jomettler/SaladFork-Experimental/InvertedMountDirectionAB/STL/Lower_B.stl

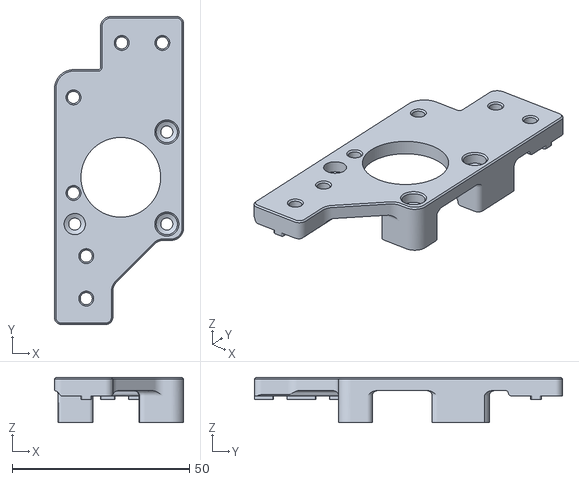
[picture p18: CAD file, 2022-04-01]
InvertedMountDirectionAB/STL/Lower_B.stl
36.5 x 87.0 x 12.8
