jomettler/SaladFork-Experimental/K3Style_Top/STL/Top/corner_10mm_x4.stl

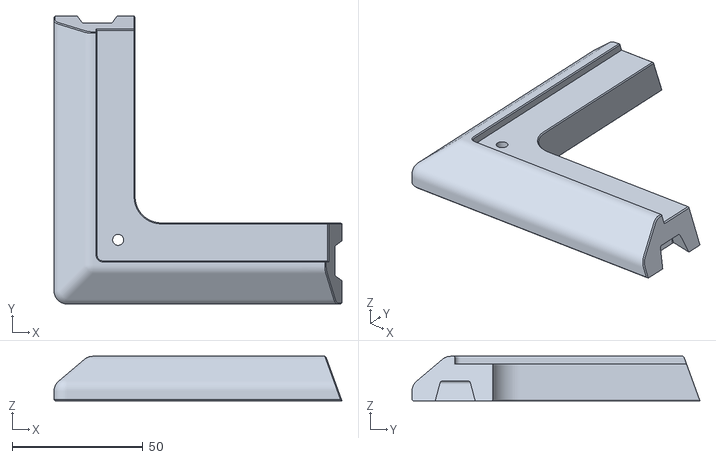
[picture p19: CAD file, 2022-04-12]
K3Style_Top/STL/Top/corner_10mm_x4.stl
110.0 x 110.0 x 17.0
