jomettler/SaladFork-Experimental/QuadAB/CAD/NOIdler_FrontDrives.step

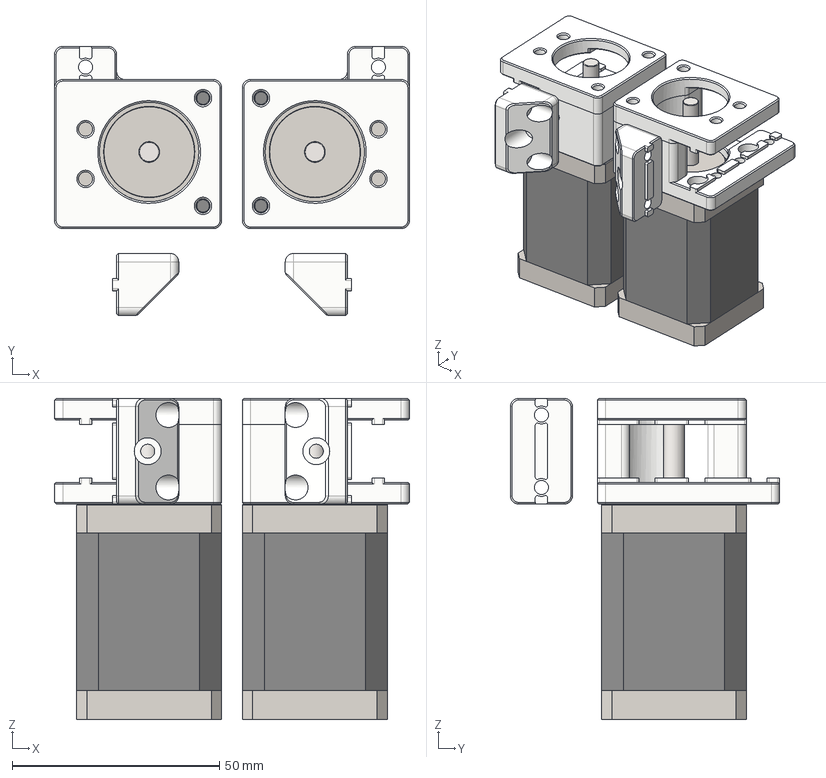
[picture p20: CAD file, 2022-04-17]
QuadAB/CAD/NOIdler_FrontDrives.step
85.7 x 65.0 x 77.5 mm
nema14_base (1) x 2
nema14_centro (1) x 2
nema14_eje (1) x 2
nema14_techo (1) x 2
