jomettler/SaladFork-Experimental/QuadAB/STL/A_Drive_Frame_Lower.stl

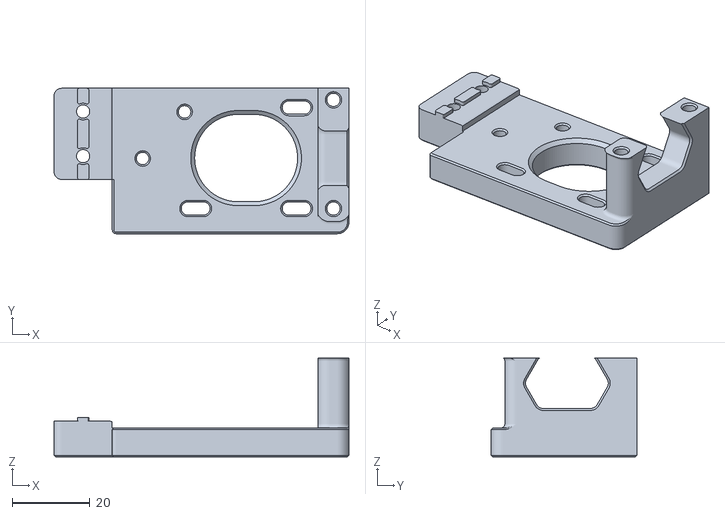
[picture p21: CAD file, 2022-03-22]
QuadAB/STL/A_Drive_Frame_Lower.stl
76.0 x 37.5 x 25.5
