jomettler/SaladFork-Experimental/QuadAB/STL/NoIdler_Front/A_Tension.stl

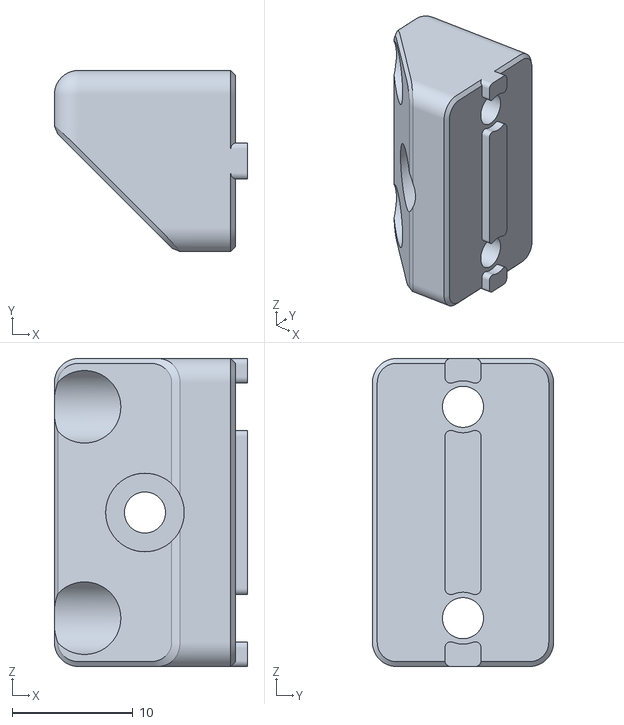
[picture p22: CAD file, 2022-04-17]
QuadAB/STL/NoIdler_Front/A_Tension.stl
16.0 x 15.0 x 25.5
