jomettler/SaladFork-Experimental/QuadAB/STL/XYJoints/XYJoint_left_bottom.stl

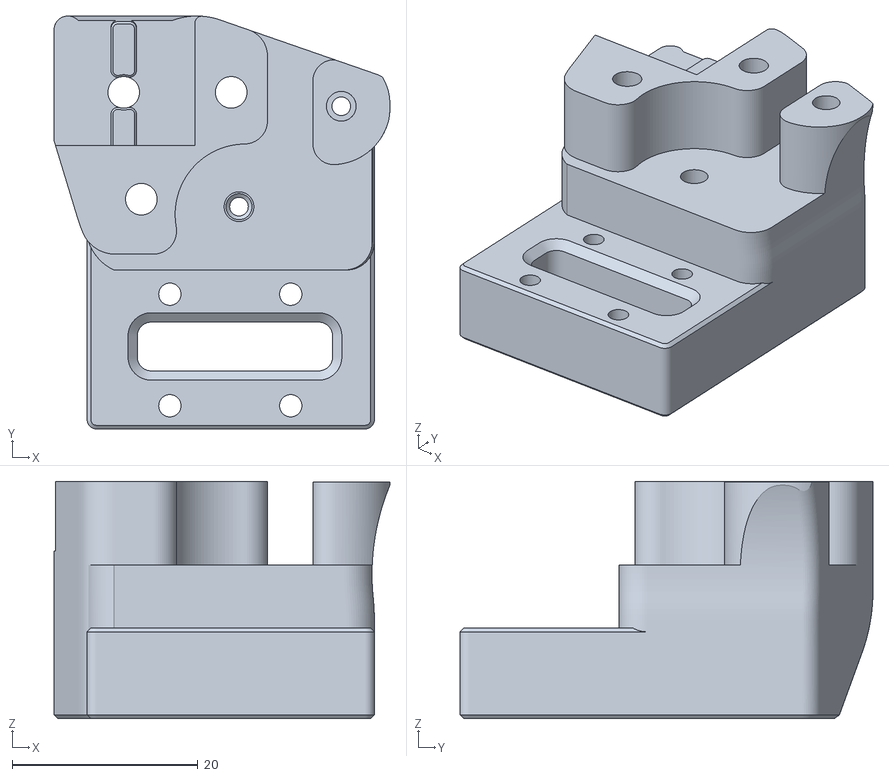
[picture p23: CAD file, 2022-03-22]
QuadAB/STL/XYJoints/XYJoint_left_bottom.stl
36.1 x 44.4 x 25.5
