jomettler/SaladFork-Experimental/QuadAB/CAD/XY-Joint_Left.step

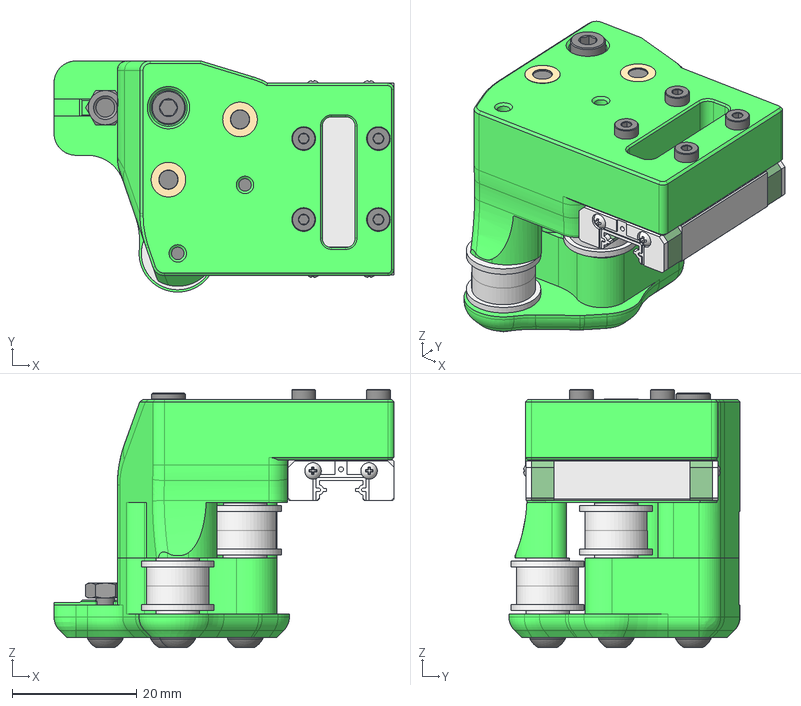
[picture p24: CAD file, 2022-03-22]
QuadAB/CAD/XY-Joint_Left.step
54.6 x 37.1 x 41.5 mm
MGN7-H-1 (3) (1)
f623-rs (1) (2) x 2
M3 washer-1 (1) (4) (1) x 2
f623-rs (2) x 2
M3 washer-1 (2) x 2
M3x8 BHCS (2) x 2
M3x35 SHCS (1) (1) x 2
M3 Threaded Insert Short.step v1 (11) (1) x 2
M2x12 SHCS v1 v1 (1) x 4
M3x25 BHCS v2 (3) x 2
M3x20 SHCS v1 (1) (2)
M3_Hex_Nut v1 (18) (1) x 3
