jomettler/SaladFork-Experimental/QuadAB/STL/B_Drive_Frame_Holder.stl

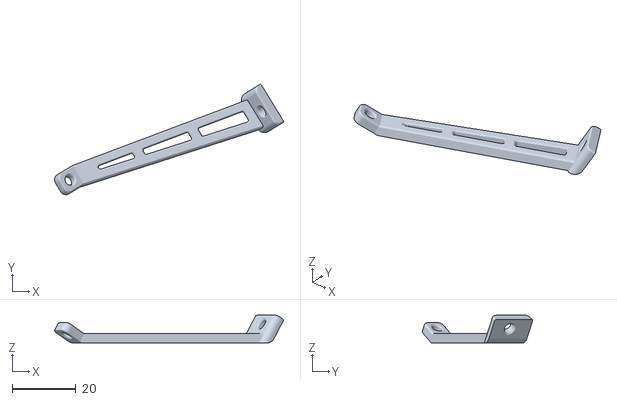
[picture p25: CAD file, 2022-03-22]
QuadAB/STL/B_Drive_Frame_Holder.stl
71.9 x 34.7 x 8.76
