jomettler/SaladFork-Experimental/QuadAB/STL/NoIdler_Front/A_Top.stl

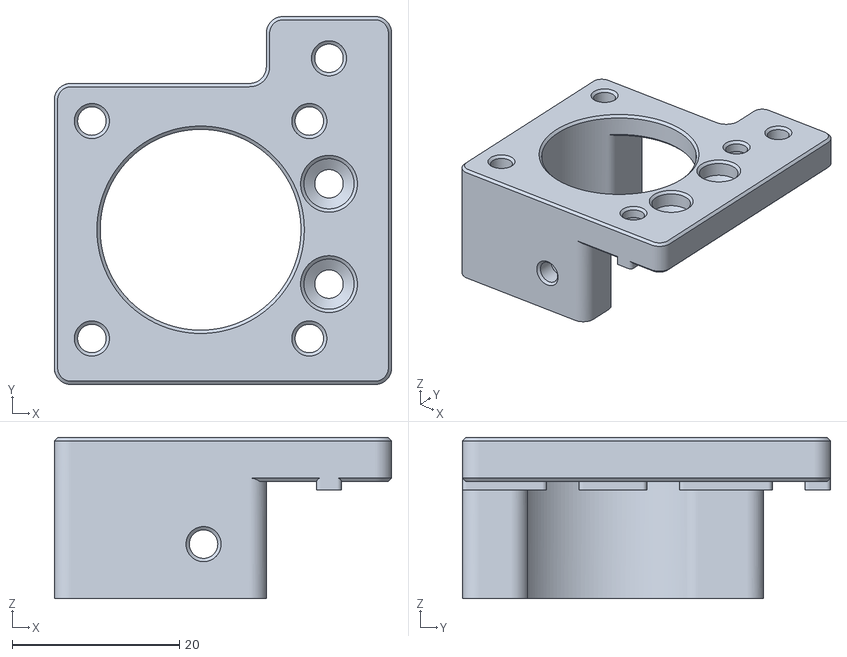
[picture p26: CAD file, 2022-04-17]
QuadAB/STL/NoIdler_Front/A_Top.stl
40.4 x 44.0 x 19.2
