jomettler/SaladFork-Experimental/QuadAB/STL/XYJoints/XYJoint_right_top.stl

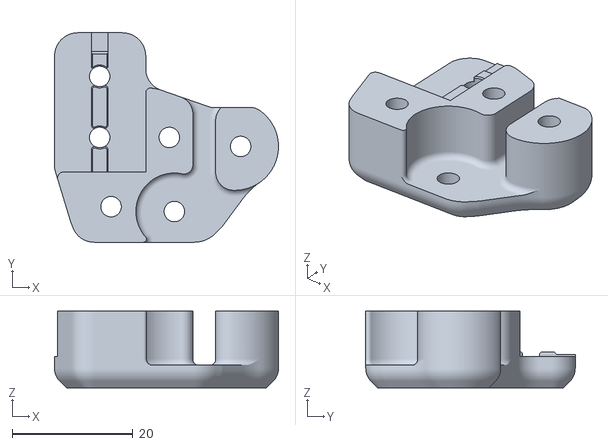
[picture p27: CAD file, 2022-03-22]
QuadAB/STL/XYJoints/XYJoint_right_top.stl
37.2 x 34.8 x 12.8
