jomettler/SaladFork-Experimental/InvertedMountDirectionAB/STL/Upper_B.stl

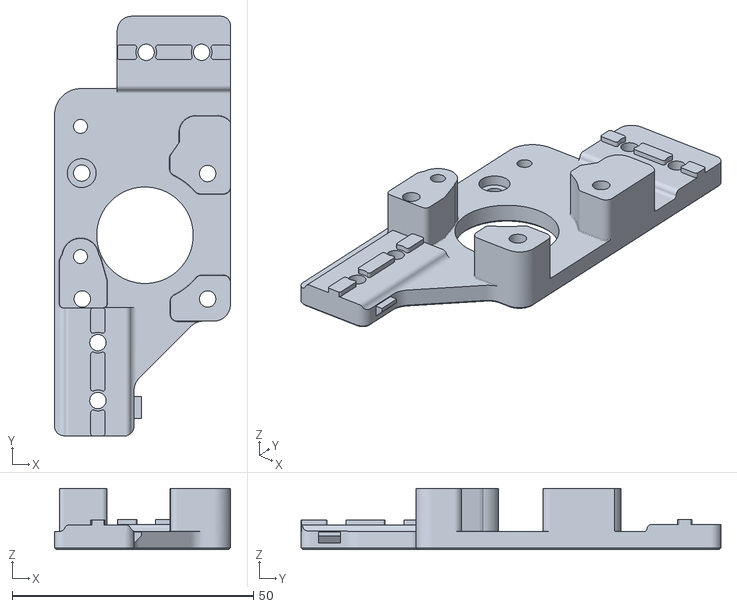
[picture p28: CAD file, 2022-04-01]
InvertedMountDirectionAB/STL/Upper_B.stl
36.5 x 87.0 x 12.8
