jomettler/SaladFork-Experimental/K3Style_Top/STL/Top/Short_x2.stl

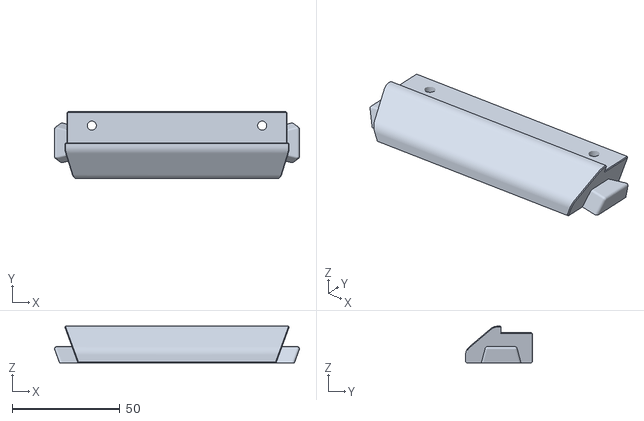
[picture p29: CAD file, 2022-04-12]
K3Style_Top/STL/Top/Short_x2.stl
113.6 x 31.0 x 17.0
