jomettler/SaladFork-Experimental/QuadAB/CAD/XY-Joint_Right.step

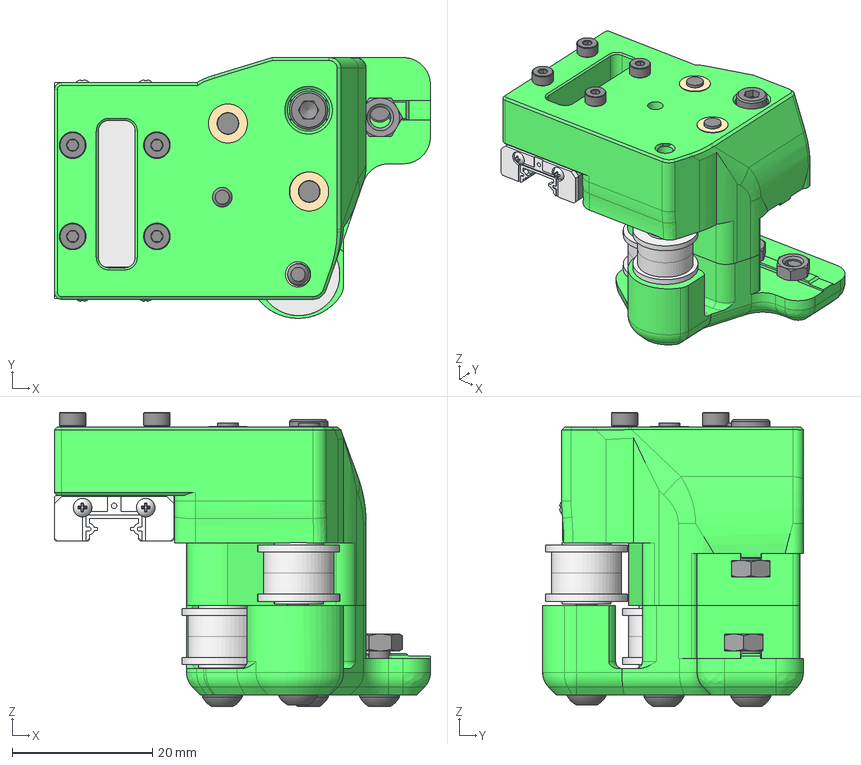
[picture p30: CAD file, 2022-03-22]
QuadAB/CAD/XY-Joint_Right.step
53.6 x 37.2 x 42.0 mm
MGN7-H-1 (1)
f623-rs (1)(Mirror) (1) x 2
M3 washer-1 (1)(Mirror) (1) x 2
f623-rs(Mirror) (1) x 2
M3 washer-1(Mirror) (1) x 2
M3 Threaded Insert Short.step v1(Mirror) (1) x 2
M3x8 BHCS (1) (1) x 2
M3x35 SHCS (1) x 2
M3x20 SHCS (1)
M2x12 SHCS v1 (1) x 4
M3x25 BHCS v2 (1) (1)
M3x25 BHCS v2 (2) (1)
M3_Hex_Nut v1 (19) (1) x 3
