jomettler/SaladFork-Experimental/QuadAB/STL/B_Drive_Tensioner.stl

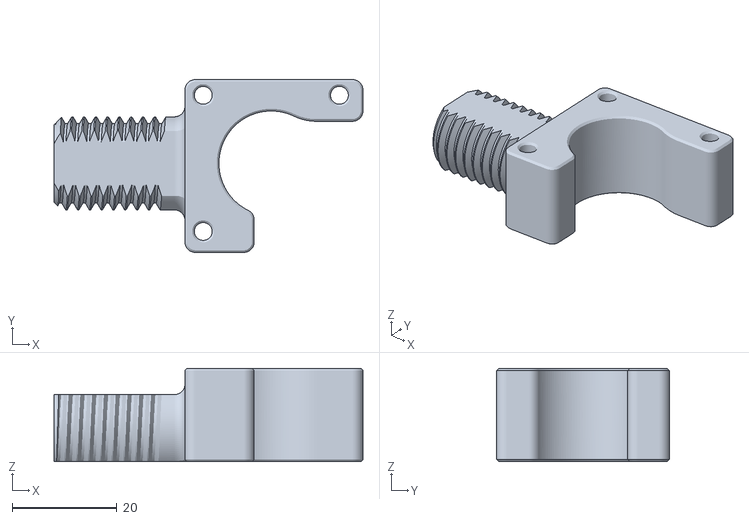
[picture p31: CAD file, 2022-03-22]
QuadAB/STL/B_Drive_Tensioner.stl
59.0 x 33.0 x 17.8
