jomettler/SaladFork-Experimental/QuadAB/STL/Back/BUpper.stl

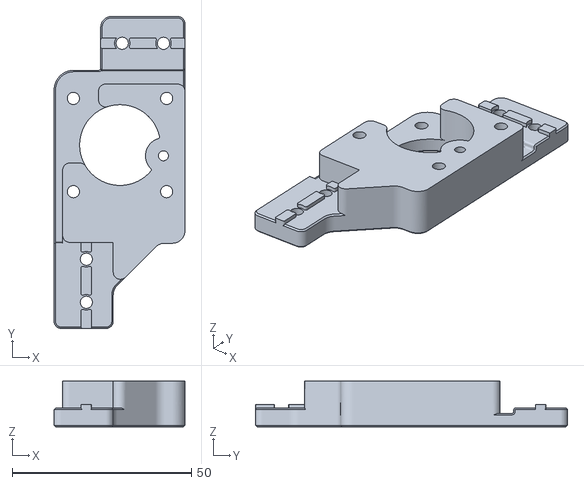
[picture p32: CAD file, 2022-04-17]
QuadAB/STL/Back/BUpper.stl
36.5 x 87.0 x 12.8
