jomettler/SaladFork-Experimental/QuadAB/STL/XYJoints/XYJoint_right_bottom.stl

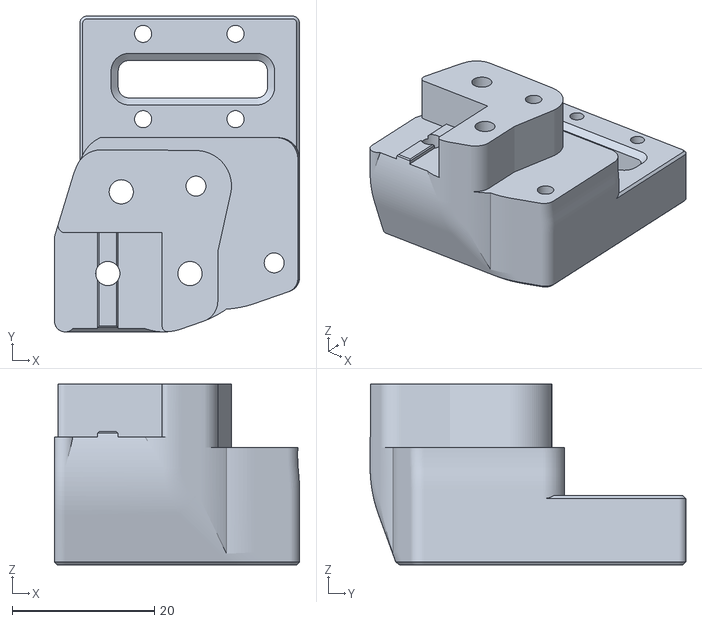
[picture p33: CAD file, 2022-03-22]
QuadAB/STL/XYJoints/XYJoint_right_bottom.stl
34.5 x 44.4 x 25.4
