jomettler/SaladFork-Experimental/QuadAB/STL/B_Tensioner_Knob.stl

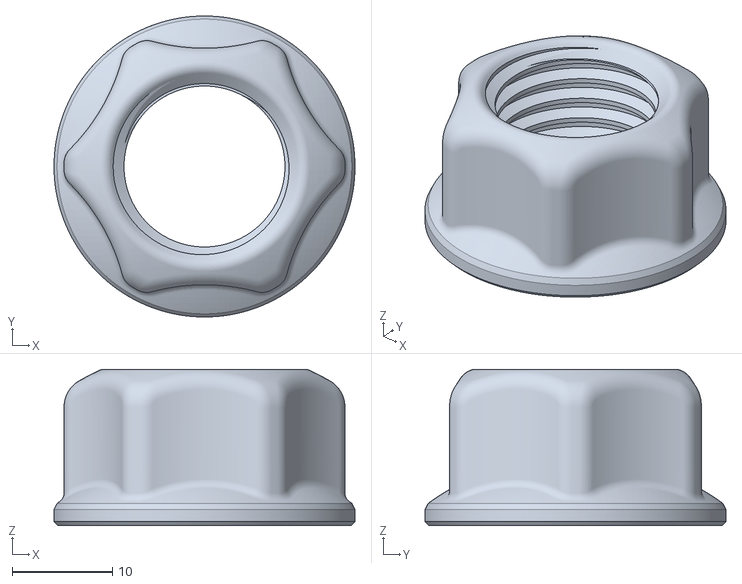
[picture p34: CAD file, 2022-03-22]
QuadAB/STL/B_Tensioner_Knob.stl
30.0 x 30.0 x 15.6
