jomettler/SaladFork-Experimental/QuadAB/STL/9mm_Spacer_x4.stl

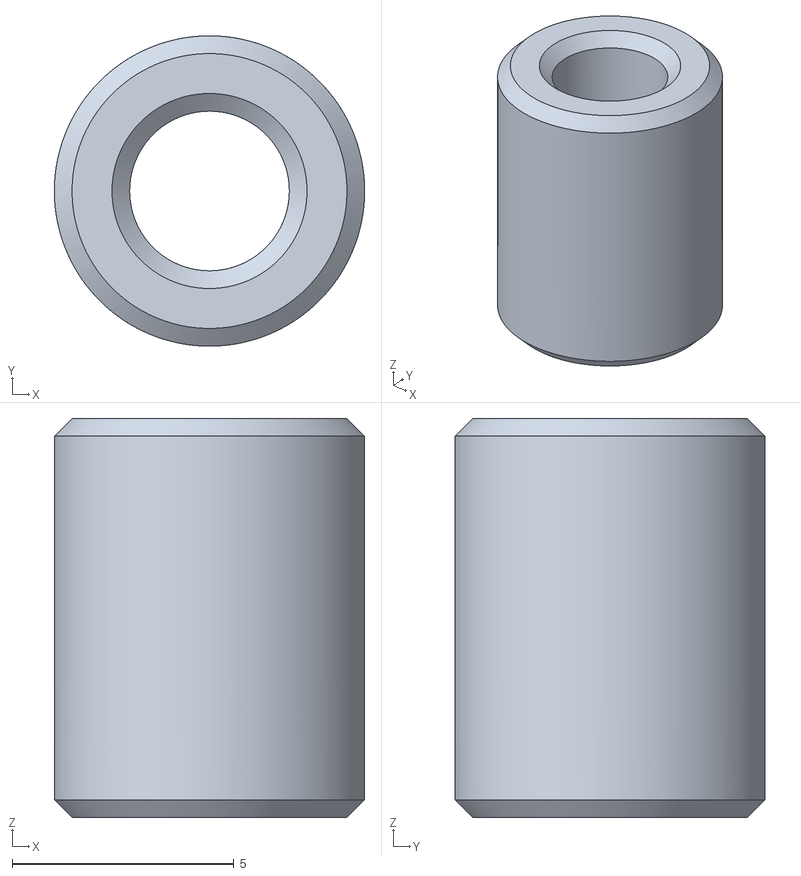
[picture p35: CAD file, 2022-03-22]
QuadAB/STL/9mm_Spacer_x4.stl
7.00 x 7.00 x 9.00
