jomettler/SaladFork-Experimental/QuadAB/STL/A_Drive_Frame_Holder.stl

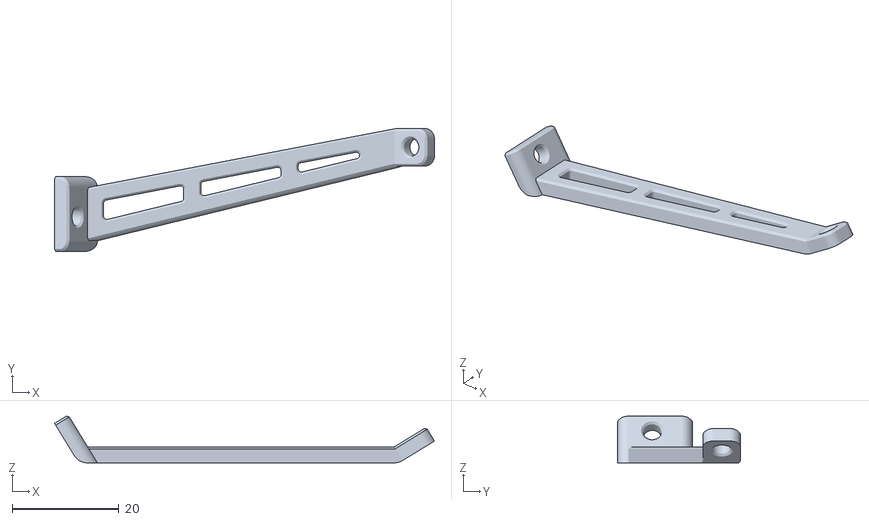
[picture p36: CAD file, 2022-03-22]
QuadAB/STL/A_Drive_Frame_Holder.stl
71.2 x 23.0 x 8.76
