jomettler/SaladFork-Experimental/QuadAB/STL/B_Drive_Frame_Upper.stl

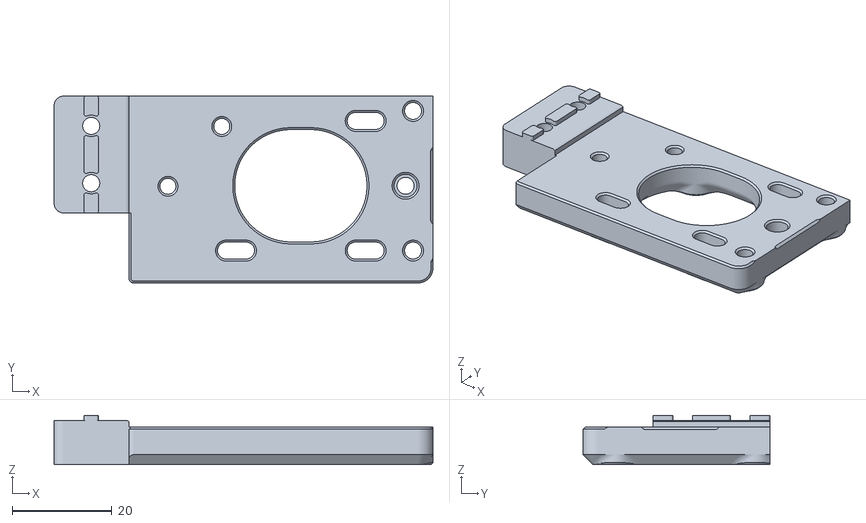
[picture p37: CAD file, 2022-03-22]
QuadAB/STL/B_Drive_Frame_Upper.stl
76.0 x 37.5 x 9.88
